PuurfectDev-MD/Near365/Firmware/Tests/flash_wav.py

# The MIT License (MIT)
# Copyright (c) 2022 Mike Teachman
# https://opensource.org/licenses/MIT

# Purpose:  Play a WAV audio file out of a speaker or headphones
#
# - read audio samples from a WAV file stored on internal flash memory
# - write audio samples to an I2S amplifier or DAC module
# - the WAV file will play continuously in a loop until
#   a keyboard interrupt is detected or the board is reset
#
# Blocking version
# - the write() method blocks until the entire sample buffer is written to I2S
#
# Use a tool such as rshell or ampy to copy the WAV file "side-to-side-8k-16bits-stereo.wav"
# to internal flash memory. The Thonny IDE also offers an easy way to copy this file (View->Files, `Upload to /` option).


import os
from machine import I2S
from machine import Pin



I2S_DOUT = 7
I2S_BCLK =6
I2S_LRC =5

I2C_DIN =15

if os.uname().machine.count("PYBv1"):

    # ======= I2S CONFIGURATION =======
    SCK_PIN = "Y6"
    WS_PIN = "Y5"
    SD_PIN = "Y8"
    I2S_ID = 2
    BUFFER_LENGTH_IN_BYTES = 5000
    # ======= I2S CONFIGURATION =======

elif os.uname().machine.count("PYBD"):
    import pyb

    pyb.Pin("EN_3V3").on()  # provide 3.3V on 3V3 output pin

    # ======= I2S CONFIGURATION =======
    SCK_PIN = "Y6"
    WS_PIN = "Y5"
    SD_PIN = "Y8"
    I2S_ID = 2
    BUFFER_LENGTH_IN_BYTES = 5000
    # ======= I2S CONFIGURATION =======

elif os.uname().machine.count("ESP32"):

    # ======= I2S CONFIGURATION =======
    SCK_PIN = 32
    WS_PIN = 25
    SD_PIN = 33
    I2S_ID = 0
    BUFFER_LENGTH_IN_BYTES = 5000
    # ======= I2S CONFIGURATION =======

elif os.uname().machine.count("Raspberry"):

    # ======= I2S CONFIGURATION =======
    SCK_PIN = 16
    WS_PIN = 17
    SD_PIN = 18
    I2S_ID = 0
    BUFFER_LENGTH_IN_BYTES = 5000
    # ======= I2S CONFIGURATION =======

elif os.uname().machine.count("MIMXRT"):

    # ======= I2S CONFIGURATION =======
    SCK_PIN = 4
    WS_PIN = 3
    SD_PIN = 2
    I2S_ID = 2
    BUFFER_LENGTH_IN_BYTES = 5000
    # ======= I2S CONFIGURATION =======

else:
    print("Warning: program not tested with this board")

# ======= AUDIO CONFIGURATION =======
WAV_FILE = "wav_file.wav"
WAV_SAMPLE_SIZE_IN_BITS = 16
FORMAT = I2S.STEREO
SAMPLE_RATE_IN_HZ = 8000
# ======= AUDIO CONFIGURATION =======

audio_out = I2S(
    I2S_ID,
    sck=Pin(I2S_BCLK),
    ws=Pin(I2S_LRC),
    sd=Pin(I2S_DOUT),
    mode=I2S.TX,
    bits=WAV_SAMPLE_SIZE_IN_BITS,
    format=FORMAT,
    rate=SAMPLE_RATE_IN_HZ,
    ibuf=BUFFER_LENGTH_IN_BYTES,
)

wav = open(WAV_FILE, "rb")
pos = wav.seek(44)  # advance to first byte of Data section in WAV file

# allocate sample array
# memoryview used to reduce heap allocation
wav_samples = bytearray(1000)
wav_samples_mv = memoryview(wav_samples)

# continuously read audio samples from the WAV file
# and write them to an I2S DAC
print("==========  START PLAYBACK ==========")
try:
    while True:
        num_read = wav.readinto(wav_samples_mv)
        # end of WAV file?
        if num_read == 0:
            # end-of-file, advance to first byte of Data section
            _ = wav.seek(44)
        else:
            _ = audio_out.write(wav_samples_mv[:num_read])

except (KeyboardInterrupt, Exception) as e:
    print("caught exception {} {}".format(type(e).__name__, e))

# cleanup
wav.close()
audio_out.deinit()
print("Done")
